JimSmiley/Magnepins/Unity/arrayTest/Assets/heart.PNG

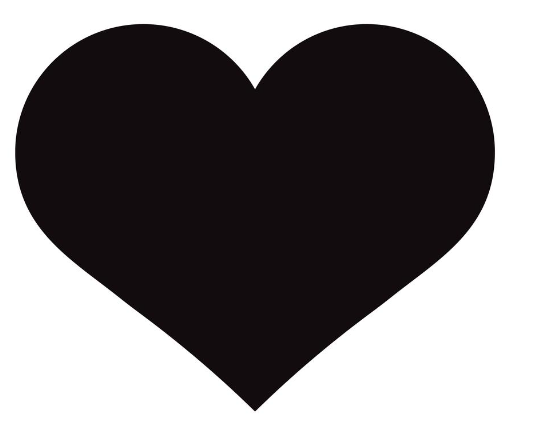
Unity/arrayTest/Assets/heart.PNG
