JimSmiley/Magnepins/Unity/arrayTest/Assets/PHI 1.PNG

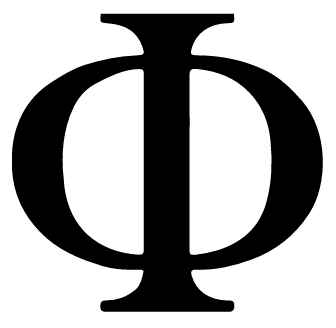
Unity/arrayTest/Assets/PHI 1.PNG
