JimSmiley/Magnepins/Unity/arrayTest/Assets/psi.PNG

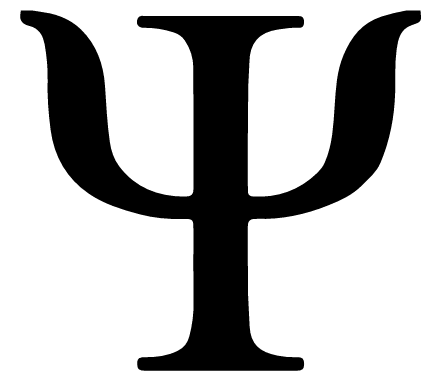
Unity/arrayTest/Assets/psi.PNG
