JimSmiley/Magnepins/Unity/arrayTest/Assets/Rho.PNG

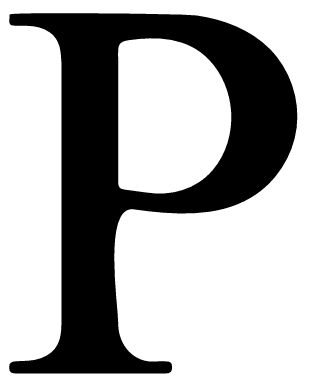
Unity/arrayTest/Assets/Rho.PNG
