JimSmiley/Magnepins/Unity/arrayTest/Assets/smileyHeart.jpg

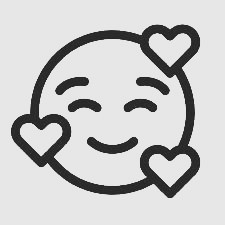
Unity/arrayTest/Assets/smileyHeart.jpg
