JimSmiley/Magnepins/Unity/arrayTest/Assets/biohazard.PNG

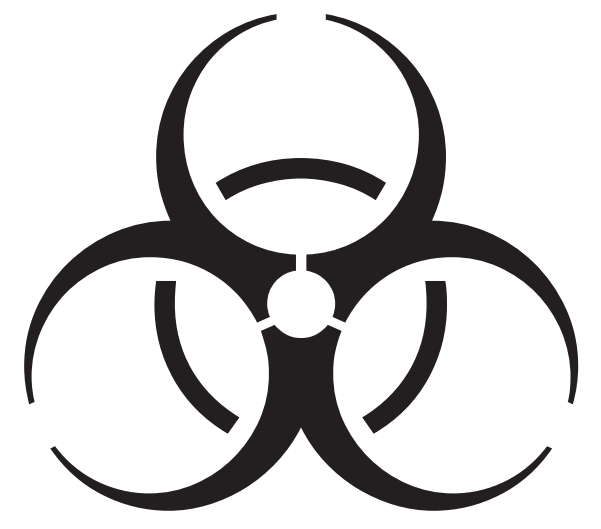
Unity/arrayTest/Assets/biohazard.PNG
